Sailowtech/Sailowtech-CTD/software/sailowtech_ctd/types_/common.py

from enum import StrEnum


class DataFields(StrEnum):
    TIMESTAMP = "timestamp"
    DATE = "date"
    PRESSURE_MBA = "pressure (mba)"
    DEPTH_METERS = "calculated depth (m)"
    TEMPERATURE = "temperature (°C)"
